MoMu-Antwerp/MuMo-v1/Dashboard/documentation/database.png

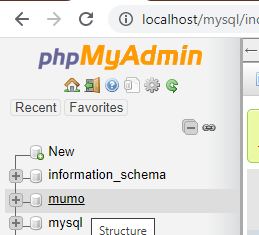
Dashboard/documentation/database.png
