MoMu-Antwerp/MuMo-v1/Dashboard/documentation/endpoint.png

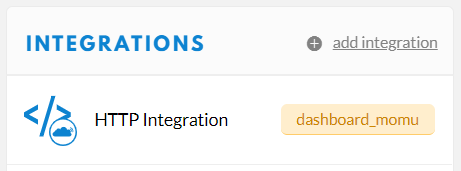
Dashboard/documentation/endpoint.png
