MoMu-Antwerp/MuMo-v1/Dashboard/documentation/login.png

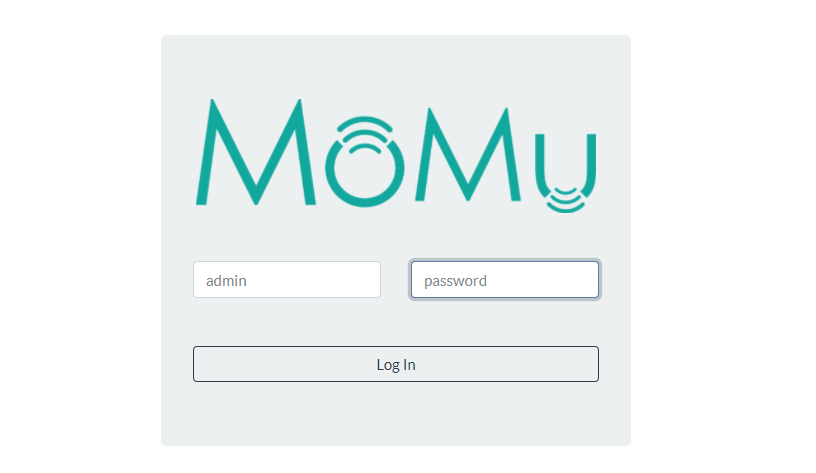
Dashboard/documentation/login.png
