MoMu-Antwerp/MuMo-v1/Dashboard/documentation/open_phpMyAdmin.png

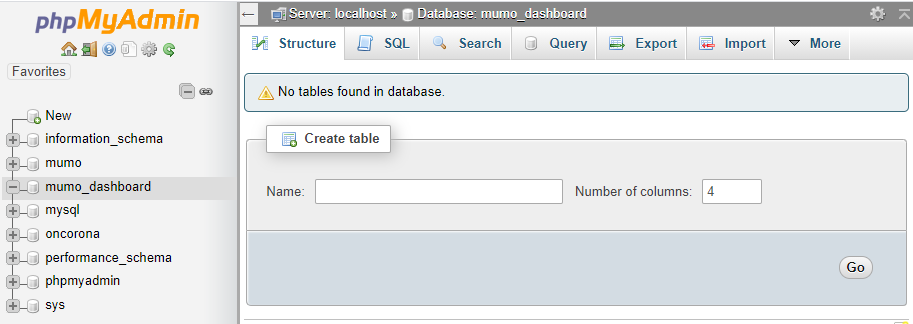
Dashboard/documentation/open_phpMyAdmin.png
