MoMu-Antwerp/MuMo-v1/documentation/ADF.png

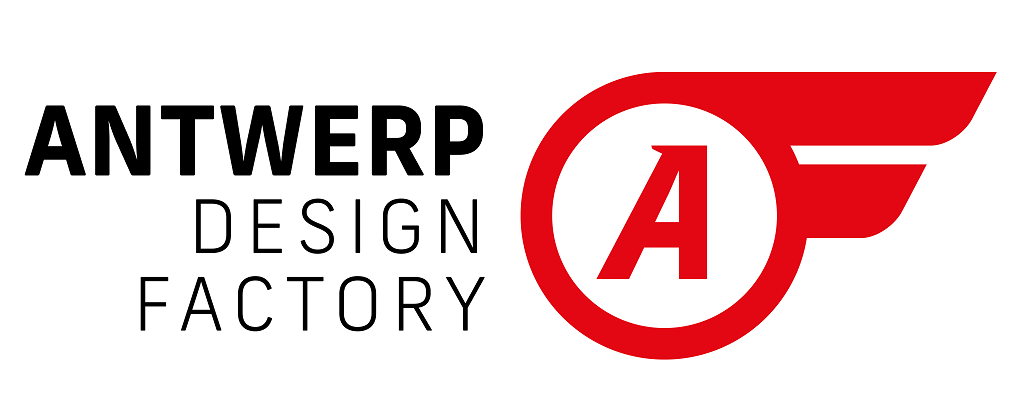
documentation/ADF.png
