MoMu-Antwerp/MuMo-v1/documentation/momu.png

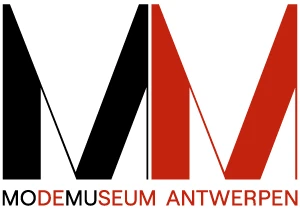
documentation/momu.png
