MoMu-Antwerp/MuMo-v1/Gateway/documentation/7_8.jpg

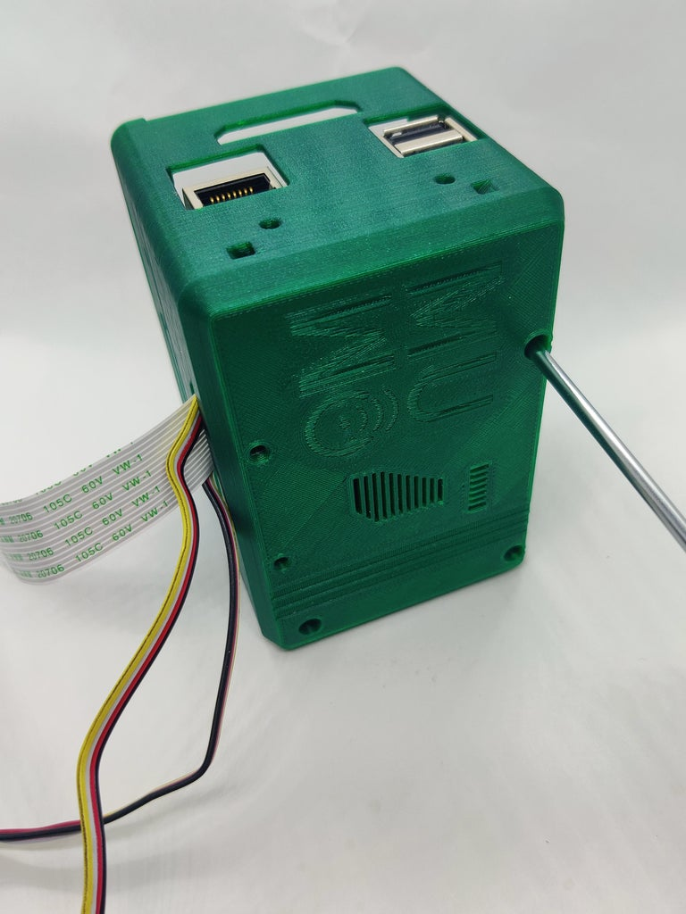
Gateway/documentation/7_8.jpg
