MoMu-Antwerp/MuMo-v1/Gateway/documentation/7_9.jpg

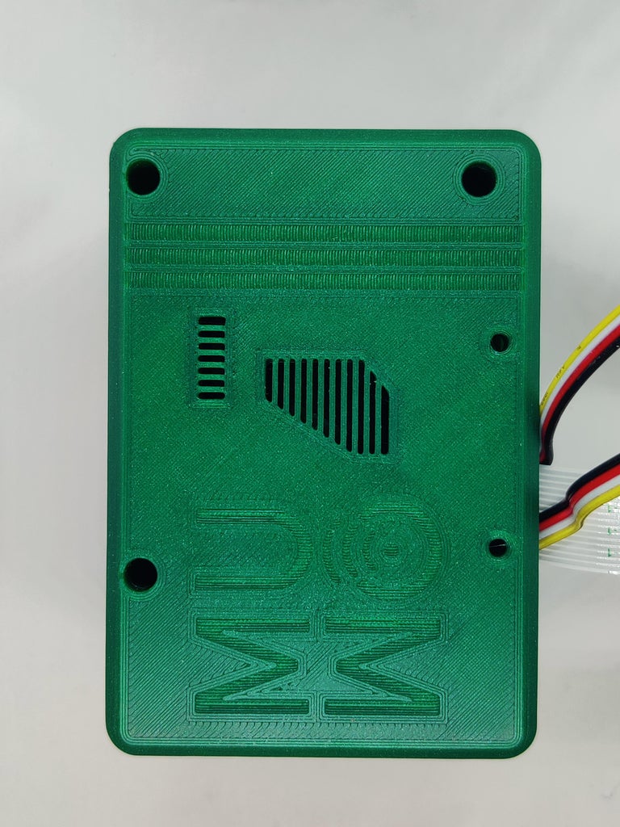
Gateway/documentation/7_9.jpg
