MoMu-Antwerp/MuMo-v1/Node/documentation/20_2.jpg

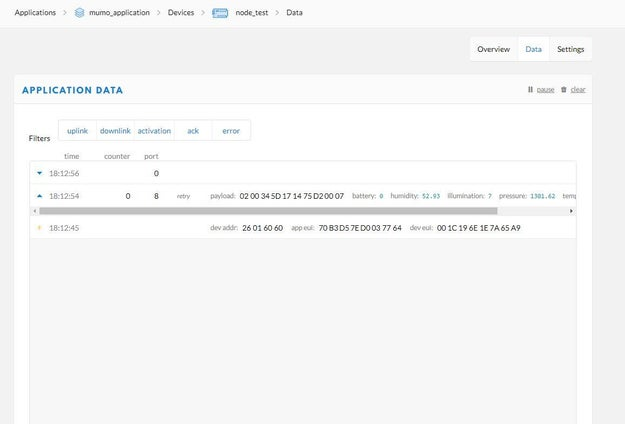
Node/documentation/20_2.jpg
